BatY0/OmniDeck/3ModelFilles/ImagesFromPrototypes/V3/ShellAssembled.jpg

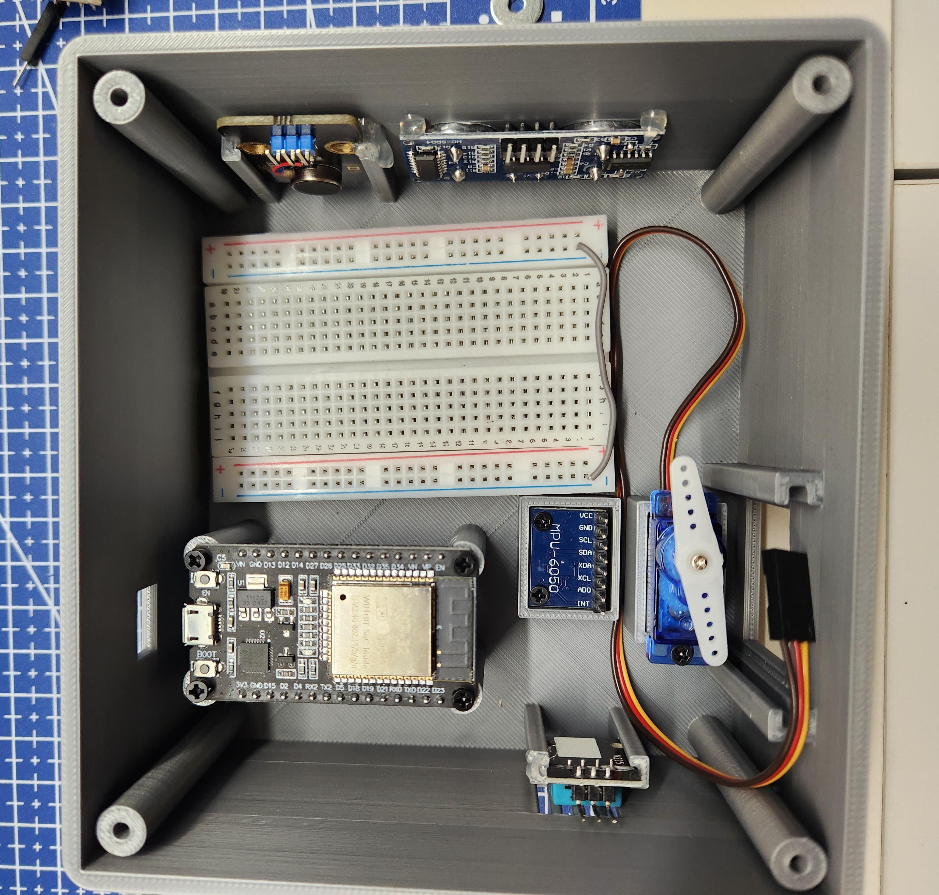
3ModelFilles/ImagesFromPrototypes/V3/ShellAssembled.jpg
