BatY0/OmniDeck/Sensor Test/OLedTest/OLedTest.ino

#include <Wire.h>
#include <Adafruit_GFX.h>
#include <Adafruit_SSD1306.h>

#define SCREEN_WIDTH 128
#define SCREEN_HEIGHT 64
Adafruit_SSD1306 display(SCREEN_WIDTH, SCREEN_HEIGHT, &Wire, -1);

void setup() {
  if(!display.begin(SSD1306_SWITCHCAPVCC, 0x3C)) {
    while(1);
  }
  
  display.clearDisplay();
  // Tüm ekranı beyaz doldur
  display.fillScreen(WHITE); 
  display.display();
}

void loop() {
  // Sadece bembeyaz yanacak
}
