BatY0/OmniDeck/3ModelFilles/ImagesFromPrototypes/V3/LidAssembledBack.jpg

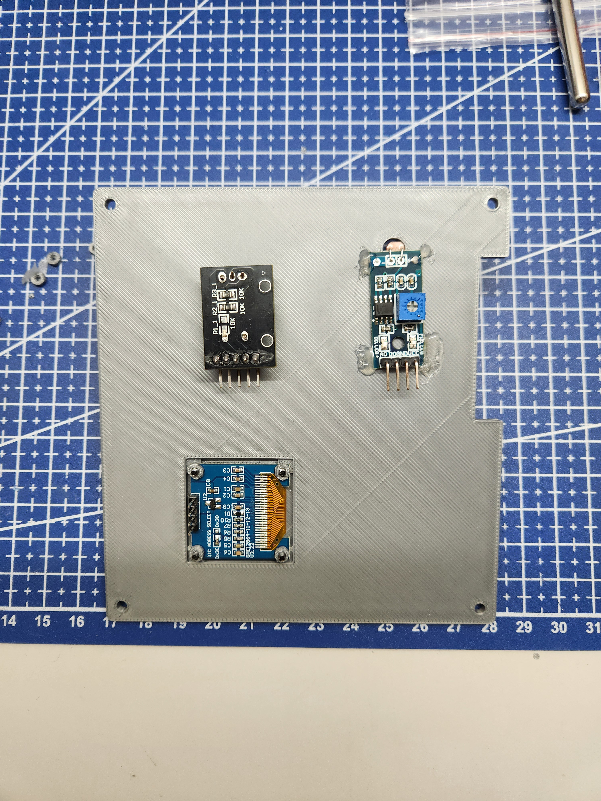
3ModelFilles/ImagesFromPrototypes/V3/LidAssembledBack.jpg
